0x000f1/lora-ch1/firmware/src/drivers/power/battery.cpp

#include "battery.h"
#include "utils/log_helper.h"
#include "drivers/ui/haptic.h"

#define TAG "POWER"

#define PIN_BATTERY_ADC 0
#define PIN_BATTERY_CHARGE 20

PowerProfile BatteryManager::currentProfile = PowerProfile::BALANCED; // Default profile

// Variables for handleBattery
static bool lastChargingState = false;
static bool lowBatteryAlerted = false;
static unsigned long lastBatteryCheckTime = 0;
const unsigned long BATTERY_CHECK_INTERVAL = 5000;

void BatteryManager::setupBattery() {
    LOG_I(TAG, "Initializing Battery Manager...");
    analogSetPinAttenuation(PIN_BATTERY_ADC, ADC_11db);
    pinMode(PIN_BATTERY_CHARGE, INPUT_PULLUP);
    lastChargingState = isCharging();
}

void BatteryManager::handleBattery() {
    bool currentChargingState = isCharging();

    if (currentChargingState != lastChargingState) {
        if (currentChargingState) {
            LOG_I(TAG, "Charger connected.");
            HapticManager::playEffect(96);
            lowBatteryAlerted = false;
        } else {
            LOG_I(TAG, "Charger disconnected.");
        }
        lastChargingState = currentChargingState;
    }

    unsigned long currentMillis = millis();
    if (currentMillis - lastBatteryCheckTime >= BATTERY_CHECK_INTERVAL) {
        lastBatteryCheckTime = currentMillis;

        uint8_t batLevel = getBatteryPercentage();

        // If the level is below 15 percent, AND not charging
        if (batLevel <= 15 && !currentChargingState && !lowBatteryAlerted) {
            HapticManager::playEffect(70); // Send a haptic signal
            lowBatteryAlerted = true;
            LOG_W(TAG, "Low battery warning: %d%%", batLevel);
        } else if (batLevel > 20 || currentChargingState) {
            lowBatteryAlerted = false; // Cancel the alert if any condition changed
        }
    }
}

void BatteryManager::setPowerProfile(PowerProfile profile) {
    currentProfile = profile;
    uint32_t cpuFreq = 80; // Default to BALANCED

    switch (profile) {
        case PowerProfile::BATTERY_SAVER:   cpuFreq = 80; break;
        case PowerProfile::BALANCED:        cpuFreq = 80; break;
        case PowerProfile::PERFORMANCE:     cpuFreq = 160; break;
    }
    setCpuFrequencyMhz(cpuFreq);
    LOG_I(TAG, "Power profile: %s | CPU: %d MHz", getPowerProfile(), cpuFreq);
}

const char* BatteryManager::getPowerProfile() {
    switch (currentProfile) {
        case PowerProfile::BATTERY_SAVER: return "BATTERY_SAVER";
        case PowerProfile::BALANCED: return "BALANCED";
        case PowerProfile::PERFORMANCE: return "PERFORMANCE";
        default: return "UNKNOWN";
    }
}

bool BatteryManager::isCharging() {
    // The BQ24075 open drain ouput is LOW when CHARING
    return digitalRead(PIN_BATTERY_CHARGE) == LOW;
}

uint8_t BatteryManager::getBatteryPercentage() {
    // analogReadMilliVolts is more advanced than analogRead
    uint32_t adcMilliVolts = analogReadMilliVolts(PIN_BATTERY_ADC);

    // The measured voltage is the half of the battery's.
    float voltageBattery = (adcMilliVolts * 2.0f) / 1000.0f;

    // Calculate the percentage (3.4 - 4.2 V range)
    float percentageBattery = ((voltageBattery - 3.4f) / (4.2f - 3.4f)) * 100.0f;

    // Handling limits and measurement errors
    if (percentageBattery > 100.0f) percentageBattery = 100.0f;
    if (percentageBattery < 0.0f) percentageBattery = 0.0f;

    return (uint8_t)percentageBattery;
}
