0x000f1/lora-ch1/firmware/src/drivers/ui/haptic.h

/**
 * @file haptic.h
 * @brief Haptic feedback functions with DRV2605L motor driver.
 * @details This component will handle the initialization and control of the motor driver.
 */

#ifndef HAPTIC_H
#define HAPTIC_H

#include <Arduino.h>
#include "SensorDRV2605.hpp"
#include <freertos/FreeRTOS.h>
#include <freertos/timers.h>

class HapticManager {
    public:
        /** 
         * @brief Initialize the Haptic driver.
         * @return 0 on success, error code on failure.
         * @details See haptic.cpp for pin configuration and initialization steps.
         */
        static int setupHaptic();
        /**
         * @brief Toggles the haptic feedback.
         * @param enableFeedback True: Feedback ON, False: Feedback OFF (Device silenced)
         */
        static bool isEnabledByUser(bool enabledFeedback);
        /**
         * @brief Play a haptic effect.
         * @param effectNumber The number selects the effect to be played. See DRV2605L documentation for effect numbers.
         * @details This function will play the specified haptic effect on the motor driver.
         */
        static void playEffect(uint8_t effectId);
    private:
        static SensorDRV2605 drv;
        // Timer to power off the DRV2605 to reduce consumption
        static TimerHandle_t powerOffTimer;
        static void powerOffTimerCallback(TimerHandle_t xTimer);
};
#endif
